hackerspace-silesia/Smogomierz/html/html-content.h

#ifdef ARDUINO_ARCH_ESP8266
#include <avr/pgmspace.h>
#endif

static const char WEB_PAGE_HEADER_CSS[] PROGMEM = "<link rel='stylesheet' href='https://rawcdn.githack.com/hackerspace-silesia/Smogomierz/b1e4dd9a2b6fddb63da88c46ef934509ab1def44/css/smogly.css'>";
// via http://raw.githack.com 
//static const char WEB_PAGE_HEADER_CSS[] PROGMEM = "<link rel='stylesheet' href='https://raw.githubusercontent.com/hackerspace-silesia/Smogomierz/master/css/smogly.css'>";
// https://raw.githubusercontent.com/hackerspace-silesia/Smogomierz/dev/src/css/smogly.css
// based on bootstrap.min.css - 4.4.1 and Bootswatch v4.4.1
// https://raw.githack.com

#ifdef ARDUINO_ARCH_ESP8266
const char WEB_PAGE_HEADER[] PROGMEM = R"rawliteral(<html lang='{Language}'><head><meta charset='utf-8'><meta name='viewport' content='width=device-width, initial-scale=1, shrink-to-fit=no'><title>Smogly - {CurrentPageTitle}</title>
{WEB_PAGE_CSS}
</head><body>
	<nav class='navbar navbar-expand-lg navbar-dark bg-dark' style='padding-left:15%'>
	<a class='navbar-brand' href='/'>Smogly</a>
	  <button class='navbar-toggler' type='button' data-toggle='collapse' data-target='#navbarColor02' aria-controls='navbarColor02' aria-expanded='false' aria-label='Toggle navigation'>
	  <span class='navbar-toggler-icon'></span>
	  </button>
	  <div class='collapse navbar-collapse' id='navbarColor02' style='padding-left:2rem'>
	    <ul class='navbar-nav mr-auto'>
	      <li class='nav-item'>
	        <a class='nav-link' href='/'>{IndexPageTitle}</a>
	      </li>
	      <li class='nav-item'>
	        <a class='nav-link' href='/config'>{ConfigPageTitle}</a>
	      </li>
		  <li class='nav-item'>
		  	<a class='nav-link' href='/update'>{UpdatePageTitle}</a>
		  </li>
	    </ul>
</div></nav>
		)rawliteral";

static const char SMOGLY_LOGO_URL[] PROGMEM = "<a class='navbar-brand' href='/'>Smogly</a>";

#elif defined ARDUINO_ARCH_ESP32
static const char WEB_PAGE_HEADER[] PROGMEM = R"rawliteral(<html lang='{Language}'><head><meta charset='utf-8'><meta name='viewport' content='width=device-width, initial-scale=1, shrink-to-fit=no'><title>Smogly - {CurrentPageTitle}</title>
{WEB_PAGE_CSS}
</head><body>
	<nav class='navbar navbar-expand-lg navbar-dark bg-dark' style='padding-left:15%'>
	<a class='navbar-brand' href='/'><img border='0' width='165' height='40' alt='SmoglyLogo' src='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'></a>
	  <button class='navbar-toggler' type='button' data-toggle='collapse' data-target='#navbarColor02' aria-controls='navbarColor02' aria-expanded='false' aria-label='Toggle navigation'>
	  <span class='navbar-toggler-icon'></span>
	  </button>
	  <div class='collapse navbar-collapse' id='navbarColor02' style='padding-left:2rem'>
	    <ul class='navbar-nav mr-auto'>
	      <li class='nav-item'>
	        <a class='nav-link' href='/'>{IndexPageTitle}</a>
	      </li>
	      <li class='nav-item'>
	        <a class='nav-link' href='/config'>{ConfigPageTitle}</a>
	      </li>
		  <li class='nav-item'>
		  	<a class='nav-link' href='/update'>{UpdatePageTitle}</a>
		  </li>
	    </ul>
</div></nav>
		)rawliteral";

static const char SMOGLY_LOGO_URL[] PROGMEM = "<a class='navbar-brand' href='/'><img border='0' width='165' height='40' alt='SmoglyLogo' src='https://raw.githubusercontent.com/hackerspace-silesia/Smogomierz/master/Smogly_Logo/SmoglyLogoTopMenu.png'></a>";
//"
#endif

#ifdef ARDUINO_ARCH_ESP8266
static const char WEB_PAGE_FOOTER[] PROGMEM = R"rawliteral(<br><hr><center><a href='http://smogly.org/' target='_blank'>Smogly</a> &#9830; <a href='https://hs-silesia.pl' target='_blank'>Hackerspace Silesia</a> &#9830;
	<script type='text/javascript'>
  		document.write(new Date().getFullYear());
	</script>
	</center></div></main></form>
			<script src='https://code.jquery.com/jquery-3.4.1.slim.min.js' integrity='sha384-J6qa4849blE2+poT4WnyKhv5vZF5SrPo0iEjwBvKU7imGFAV0wwj1yYfoRSJoZ+n' crossorigin='anonymous'></script>
			<script src='https://cdn.jsdelivr.net/npm/popper.js@1.16.0/dist/umd/popper.min.js' integrity='sha384-Q6E9RHvbIyZFJoft+2mJbHaEWldlvI9IOYy5n3zV9zzTtmI3UksdQRVvoxMfooAo' crossorigin='anonymous'></script>
			<script src='https://stackpath.bootstrapcdn.com/bootstrap/4.4.1/js/bootstrap.min.js' integrity='sha384-wfSDF2E50Y2D1uUdj0O3uMBJnjuUD4Ih7YwaYd1iqfktj0Uod8GCExl3Og8ifwB6' crossorigin='anonymous'></script>
			</body></html>
	)rawliteral";
#elif defined ARDUINO_ARCH_ESP32
static const char WEB_PAGE_FOOTER[] PROGMEM = R"rawliteral(<br><hr><center><a href='http://smogly.org/' target='_blank'>Smogly</a> &#9830; <a href='https://hs-silesia.pl' target='_blank'>Hackerspace Silesia</a> &#9830;
	<script type='text/javascript'>
  		document.write(new Date().getFullYear());
	</script>
	</center></div></main></form>
			<script src='https://code.jquery.com/jquery-3.4.1.slim.min.js' integrity='sha384-J6qa4849blE2+poT4WnyKhv5vZF5SrPo0iEjwBvKU7imGFAV0wwj1yYfoRSJoZ+n' crossorigin='anonymous'></script>
			<script src='https://cdn.jsdelivr.net/npm/popper.js@1.16.0/dist/umd/popper.min.js' integrity='sha384-Q6E9RHvbIyZFJoft+2mJbHaEWldlvI9IOYy5n3zV9zzTtmI3UksdQRVvoxMfooAo' crossorigin='anonymous'></script>
			<script src='https://stackpath.bootstrapcdn.com/bootstrap/4.4.1/js/bootstrap.min.js' integrity='sha384-wfSDF2E50Y2D1uUdj0O3uMBJnjuUD4Ih7YwaYd1iqfktj0Uod8GCExl3Og8ifwB6' crossorigin='anonymous'></script>
			</body></html>
	)rawliteral";
#endif
	
// CONFIG PAGE - Start
	const char WEB_CONFIG_PAGE_TOP[] PROGMEM = R"rawliteral(<main role='main' class='container'><div class='jumbotron'>
	<center><h1>Smogly - {TEXT_CONFIG_PAGE}</h1></center><br><br>
	)rawliteral";

	const char WEB_CONFIG_PAGE_SUBMIT_DEVICE_BUTTON[] = "<input type='submit' name='submit1' class='btn btn-outline-danger' value='{TEXT_SAVE}' /></form>";

	const char WEB_CONFIG_PAGE_SUBMIT_SERVICES_BUTTON[] = "<input type='submit' name='submit2' class='btn btn-outline-danger' value='{TEXT_SAVE}' /></form>";

	const char WEB_CONFIG_ADVANCED_MQTT_PAGE_SUBMIT_SERVICES_BUTTON[] = "<input type='submit' name='submit3' class='btn btn-outline-danger' value='{TEXT_SAVE}' /></form>";

	const char WEB_CONFIG_PAGE_SELECT[] PROGMEM = "<select name='{key}'>";

	const char WEB_CONFIG_PAGE_SELECTEND[] PROGMEM = "</select><br />";

	const char WEB_CONFIG_PAGE_ADDOPTION[] PROGMEM = "<option value='{value}' {srslyValue}{label}</option>";

	const char WEB_CONFIG_PAGE_TEXTIMPUT[] PROGMEM = "<input type='text' maxlength='255' size='20' name='{key}' value='{value}'> {postfix}<br />";

	const char WEB_CONFIG_PAGE_MQTT_TEXTIMPUT[] PROGMEM = "<input type='text' maxlength='120' size='32' name='{key}' value='{value}'>{postfix}";

	const char WEB_CONFIG_PAGE_PASSWDINPUT[] = "<input type='password' maxlength='255' size='20' name='{key}' value='{value}'> {postfix}<br />";

	const char WEB_CONFIG_PAGE_INTINPUT[] PROGMEM = "<input type='number' step='1' maxlength='255' name='{key}' value='{value}'> {postfix}<br />";

	const char WEB_CONFIG_PAGE_FLOATINPUT[] = "<input type='number' step='0.000001' maxlength='255' name='{key}' value='{value}'> {postfix}<br />";
	/*
	const char WEB_CONFIG_DEVICE_PAGE_BUTTON[] = "<a href='/config_device' class='btn btn-outline-primary btn-sm' role='button'>{TEXT_CONFIG_DEVICE_PAGE}</a>";

	const char WEB_CONFIG_SERVICES_PAGE_BUTTON[] = "<a href='/config_services' class='btn btn-outline-primary btn-sm' role='button'>{TEXT_CONFIG_SERVICES_PAGE}</a>";
	*/
	const char WEB_CONFIG_PAGE_WIFIERASE[] = "<a href='/erase_wifi' class='btn btn-outline-primary btn-sm' role='button'>{TEXT_ERASEWIFICONFIG}</a>";

	const char WEB_CONFIG_PAGE_HOMEKIT_RESET[] = "<a href='/homekit_reset' class='btn btn-outline-primary btn-sm' role='button'>{TEXT_PAGE_HOMEKIT_RESET}</a>";

	const char WEB_CONFIG_PAGE_RESTORECONFIG[] = "<a href='/restore_config' class='btn btn-outline-primary btn-sm' role='button'>{TEXT_RESTORESETTINGS}</a>";

	const char WEB_CONFIG_TOP_PAGE_INFO[] PROGMEM = R"rawliteral(<center><div class='card text-white bg-success mb-3' style='max-width: 30rem;'>
			  <div class='card-body'>
			    <h4 class='card-title'><strong>{TEXT_SAVED}!</strong></h4>
			    <p class='card-text'>{TEXT_POSTCONFIG_INFO}</p>
			  </div></div></center>)rawliteral";

// CONFIG PAGE - END
// CONFIG DEVICE PAGE - Start	
#ifdef ASYNC_WEBSERVER_ON
const char WEB_CONFIG_DEVICE_PAGE_TOP[] PROGMEM = R"rawliteral(<form method='GET' action='/config_device_save'>
	<main role='main' class='container'><div class='jumbotron'>
	<center><h1>Smogly - {TEXT_CONFIG_DEVICE_PAGE}</h1></center><br>
	<div style='color: #2f7a2d'> <strong>{TEXT_SAVED}!</strong> - {TEXT_POSTCONFIG_INFO} </div><br><hr><br>
	{TEXT_INSTRUCIONSLINK}<br><br>
	)rawliteral";
#else
const char WEB_CONFIG_DEVICE_PAGE_TOP[] PROGMEM = R"rawliteral(<form method='POST' action='/config_device'>
	<main role='main' class='container'><div class='jumbotron'>
	<center><h1>Smogly - {TEXT_CONFIG_DEVICE_PAGE}</h1></center><br>
	{WEB_CONFIG_TOP_PAGE_INFO}
	<br><hr><br>
	{TEXT_INSTRUCIONSLINK}<br><br>
	)rawliteral";
#endif
const char WEB_CONFIG_DEVICE_PAGE_SECOND_THP[] PROGMEM = R"rawliteral(
	<br>
	{TEXT_SECOND_THP_SDA_SCL} <br>
	<b>{TEXT_SECOND_THP_SDA}: </b>{SECOND_THP_SDA}
	<b>{TEXT_SECOND_THP_SCL}: </b>{SECOND_THP_SCL}
)rawliteral";

const char WEB_CONFIG_DEVICE_PAGE_CONFIG[] PROGMEM = R"rawliteral(<b>{TEXT_DEVICENAME}: </b>{device_name} <br>
	<b>{TEXT_DEVICENAMEAUTO}: </b>{DEVICENAME_AUTO}
	<b>{TEXT_SELECTEDLANGUAGE}: </b>{LanguageSelect}
	<hr>
	<b>{TEXT_TEMPHUMIPRESSSENSOR}: </b>{THP_MODELSelect}
	<b>{TEXT_PMSENSOR}: </b>{DUST_MODELSelect}
	<hr>{TEXT_FIRST_THP_SDA_SCL} - {THP_MODEL}<br>
	<b>{TEXT_FIRST_THP_SDA}: </b>{FIRST_THP_SDA}
	<b>{TEXT_FIRST_THP_SCL}: </b>{FIRST_THP_SCL}
	<br>
	<b>{TEXT_SECOND_THP}: </b>{SECOND_THP}
	{WEB_CONFIG_DEVICE_PAGE_SECOND_THP}
	<br>{TEXT_DUST_TX_RX} - {DUST_MODEL}<br>
	<b>{TEXT_DUST_TX}: </b>{DUST_TX}
	<b>{TEXT_DUST_RX}: </b>{DUST_RX}
	<hr>
	<b>{TEXT_FREQUENTMEASUREMENTONOFF}: </b>{FREQUENTMEASUREMENT_Select} {TEXT_FREQUENTMEASUREMENTINFO}<br>
	<b>{TEXT_MEASUREMENTFREQUENCY}: </b>{FREQUENTMEASUREMENT_time}
	<b>{TEXT_AVERAGELASTRESULT}: </b>{NUMBEROFMEASUREMENTS}
	<hr><b>DeepSleep: </b>{DEEPSLEEP_ON} {TEXT_DEEPSLEEPINFO}
	<hr>
	<b>{TEXT_DISPLAYPM1}: </b> {DISPLAY_PM1}
	<b>{TEXT_ALTITUDEINFO}: </b>{MYALTITUDE}
	<hr>
	<b>{TEXT_SECURECONFIGUPDATEPAGE}: </b>{CONFIG_AUTH}
	<b>{TEXT_SECURELOGIN}: </b>{CONFIG_USERNAME}
	<b>{TEXT_SECUREPASSWD}: </b>{CONFIG_PASSWORD}
	{TEXT_SECURELOGOUTINFO}
	<hr>
	<b>Debug: </b>{DEBUG}
	<b>{TEXT_CALIBMETHOD}: </b>{CalibrationModelSelect}
	<b>{TEXT_CALIB1}: </b>{calib1}
	<br>
	<!-- <b>{TEXT_CALIB2}: </b>{calib2} -->
	<b>{TEXT_SOFTWATEVERSION}: </b>{SOFTWAREVERSION}
	<br><b>{TEXT_AUTOUPDATEON}: </b>{AUTOUPDATEON} {TEXT_UPDATEPAGEAUTOUPDATEWARNING}
	<br><b>{TEXT_HOMEKIT_SUPPORT}: </b>{HOMEKIT_SUPPORT_ON}
	<b>{TEXT_HOMEKIT_IS_PAIRED}: </b>{HOMEKIT_PAIRED_RESET}
	
	<hr><center><br>
	{WiFiEraseButton}  {RestoreConfigButton}
	<br><br></center><hr><br><center>
	{SubmitButton}
	</center>
	)rawliteral";
// CONFIG DEVICE PAGE - END
// CONFIG SERVICES PAGE - Start
#ifndef ASYNC_WEBSERVER_ON
const char WEB_CONFIG_SERVICES_PAGE_TOP[] PROGMEM = R"rawliteral(<form method='POST' action='/config_services'>
	<main role='main' class='container'><div class='jumbotron'>
	<center><h1>Smogly - {TEXT_CONFIG_SERVICES_PAGE}</h1></center><br>
	{WEB_CONFIG_TOP_PAGE_INFO}
	<br><hr><br>
	{TEXT_INSTRUCIONSLINK}<br><br>
	)rawliteral";

	const char WEB_CONFIG_SERVICES_PAGE_CONFIG[] PROGMEM = R"rawliteral(<b>{TEXT_SENDINGINTERVAL}: </b>{SENDING_FREQUENCY}
		<b>{TEXT_DBSENDINGINTERVAL}: </b>{SENDING_DB_FREQUENCY}
		<hr>
		<b>{TEXT_SMOGLISTSENDING}: </b>{SMOGLIST_ON} {TEXT_SMOGLISTINFO}
		<hr>
		<b>{TEXT_LUFTDATENSENDING}: </b>{LUFTDATEN_ON}
		<b>ChipID: </b>{LUFTDATEN_ChipID}
		<br><b>{THPSENSOR}</b> Sensor PIN: <b>{THPXPIN}</b>
		<br><b>{DUSTSENSOR}</b> Sensor PIN: <b>{DUSTXPIN}</b>
		<hr>
		<b>{TEXT_AQIECOSENDING}: </b>{AQI_ECO_ON}
		<b>{TEXT_AQIECOSERVER}: </b>{AQI_ECO_HOST}
		<b>{TEXT_AQIECOPATH}: </b>{AQI_ECO_PATH}
		<b>{ESP_MODEL} ID: </b>{AQI_ECO_ChipID}
		<hr>
		<b>{TEXT_AIRMONITORSENDING}: </b>{AIRMONITOR_ON}
		<b>{TEXT_AIRMONITORCHARTS}: </b>{AIRMONITOR_GRAPH_ON}
		<b>{TEXT_AIRMONITORCOORDINATESINFO}:
		<br>{TEXT_AIRMONITORLATITUDE}: </b>{LATITUDE}
		<b>{TEXT_AIRMONITORLONGITUDE}: </b>{LONGITUDE}
		<hr>
		<b>{TEXT_THINGSPEAKSENDING}: </b>{THINGSPEAK_ON}
		<b>{TEXT_THINGSPEAKCHARTS}: </b>{THINGSPEAK_GRAPH_ON}
		<b>{TEXT_THINGSPEAK_WRITE_API_KEY}: </b>{THINGSPEAK_API_KEY}
		<b>{TEXT_THINGSPEAKCHANNELID}: </b>{THINGSPEAK_CHANNEL_ID}
		<b>{TEXT_THINGSPEAK_READ_API_KEY}: </b>{THINGSPEAK_READ_API_KEY}
		<hr>
		<b>{TEXT_INFLUXDBSENDING}: </b>{INFLUXDB_ON}
		<b>{TEXT_INFLUXDBVERSION}: </b>{INFLUXDB_VERSION}
		<b>{TEXT_INFLUXDBSERVER}: </b>{INFLUXDB_HOST}
		<b>{TEXT_INFLUXDBPORT}: </b>{INFLUXDB_PORT}
		<b>{TEXT_INFLUXDBNAME}: </b>{INFLUXDB_DATABASE}
		<b>{TEXT_INFLUXDBUSER}: </b>{INFLUXDB_USER}
		<b>{TEXT_INFLUXDBPASSWD}: </b>{INFLUXDB_PASSWORD}
		<b>{TEXT_INFLUXDBORG}: </b>{INFLUXDB_ORG}
		<b>{TEXT_INFLUXDBBUCKET}: </b>{INFLUXDB_BUCKET}
		<b>{TEXT_INFLUXDBTOKEN}: </b>{INFLUXDB_TOKEN}
		<hr>
		<br><center>{AdvancedMQTTConfigButton}</center><br>
		<hr><center><br>
		{WiFiEraseButton}  {RestoreConfigButton}
		<br><br></center><hr><br><center>
		{SubmitButton}
		</center>
		)rawliteral";
#endif
// CONFIG SERVICES PAGE - END
// CONFIG ADVANCED MQTT PAGE - Start
#ifdef ASYNC_WEBSERVER_ON
	const char WEB_CONFIG_ADVANCED_MQTT_PAGE_TOP[] PROGMEM = R"rawliteral(<form method='GET' action='/config_adv_mqtt_save'>
	<main role='main' class='container'><div class='jumbotron'>
	<center><h1>Smogly - {TEXT_ADVANCED_MQTT_PAGE}</h1></center><br>
	{WEB_CONFIG_TOP_PAGE_INFO}
	<br><hr><br>
	{TEXT_INSTRUCIONSLINK}<br><br>
	)rawliteral";
#else
	const char WEB_CONFIG_ADVANCED_MQTT_PAGE_TOP[] PROGMEM = R"rawliteral(<form method='POST' action='/config_adv_mqtt'>
	<main role='main' class='container'><div class='jumbotron'>
	<center><h1>Smogly - {TEXT_ADVANCED_MQTT_PAGE}</h1></center><br>
	{WEB_CONFIG_TOP_PAGE_INFO}
	<br><hr><br>
	{TEXT_INSTRUCIONSLINK}<br><br>
	)rawliteral";
#endif

	const char WEB_CONFIG_ADVANCED_MQTT_PAGE_CONFIG[] PROGMEM = R"rawliteral(<br><b>{TEXT_MQTTSENDING}: </b>{MQTT_ON}
		<b>{TEXT_MQTTSERVER}: </b>{MQTT_HOST}
		<b>{TEXT_MQTTPORT}: </b>{MQTT_PORT}
		<b>{TEXT_MQTTUSER}: </b>{MQTT_USER}
		<b>{TEXT_MQTTPASSWD}: </b>{MQTT_PASSWORD}
		<br>{TEXT_MQTT_TOPIC_INFO}
		<br><br>
		<b>{TEXT_MQTT_IP_IN_TOPIC}: </b>{MQTT_IP_IN_TOPIC}
		<b>{TEXT_MQTT_DEVICENAME_IN_TOPIC}: </b>{MQTT_DEVICENAME_IN_TOPIC}
		<b>{TEXT_MQTT_SLASH_AT_THE_BEGINNING}: </b>{MQTT_SLASH_AT_THE_BEGINNING}
		<b>{TEXT_MQTT_SLASH_AT_THE_END}: </b>{MQTT_SLASH_AT_THE_END}
		<br>
		<b>{TEXT_TEMP_TOPIC}: </b>/{MQTT_IP}{MQTT_DEVICENAME}{MQTT_TOPIC_TEMP}/{MQTT_TEMP}<br />
		<b>{TEXT_HUMI_TOPIC}: </b>/{MQTT_IP}{MQTT_DEVICENAME}{MQTT_TOPIC_HUMI}/{MQTT_HUMI}<br />
		<b>{TEXT_PRESS_TOPIC}: </b>/{MQTT_IP}{MQTT_DEVICENAME}{MQTT_TOPIC_PRESS}/{MQTT_PRESS}<br />
		<b>{TEXT_PM1_TOPIC}: </b>/{MQTT_IP}{MQTT_DEVICENAME}{MQTT_TOPIC_PM1}/{MQTT_PM1}<br />
		<b>{TEXT_PM25_TOPIC}: </b>/{MQTT_IP}{MQTT_DEVICENAME}{MQTT_TOPIC_PM25}/{MQTT_PM25}<br />
		<b>{TEXT_PM10_TOPIC}: </b>/{MQTT_IP}{MQTT_DEVICENAME}{MQTT_TOPIC_PM10}/{MQTT_PM10}<br />
		<b>{TEXT_AIRQUALITY_TOPIC}: </b>/{MQTT_IP}{MQTT_DEVICENAME}{MQTT_TOPIC_AIRQUALITY}/{MQTT_AIRQUALITY}<br />
		<br>
		<hr><center><br>
		{RestoreConfigButton}
		<br><br></center><hr><br><center>
		{SubmitButton}
		</center>
		)rawliteral";
		//#endif
// CONFIG ADVANCED MQTT PAGE - END
// UPDATE BUTTONS - START

const char WEB_GOTO_CONFIG_ADVANCED_MQTT_PAGE_BUTTON[] PROGMEM = "<a href='/config_adv_mqtt' class='btn btn-outline-primary btn-sm' role='button'>{TEXT_CONFIG_ADV_MQTT}</a>";

const char WEB_UPDATE_BUTTON_MANUALUPDATE[] PROGMEM = "<a href='/update' class='btn btn-outline-primary btn-sm' role='button'>{TEXT_MANUALUPDATEBUTTON}</a>";

// UPDATE BUTTONS - END
// UPDATE PAGE - START
#ifndef ASYNC_WEBSERVER_ON
const char WEB_UPDATE_PAGE_UPDATE[] PROGMEM = R"rawliteral(<main role='main' class='container'><div class='jumbotron'>
	<form id='data' action='/update' method='POST' enctype='multipart/form-data'>
	<center><h1>Smogly - {TEXT_UPDATE_PAGE}</h1></center><br><br>
	{WEB_UPDATE_INFO_WARNING}
	<br><br><div class='input-group mb-3'><div class='custom-file'><input type='file' accept='.bin' class='custom-file-input' id='inputGroupFile04' name='update'><label class='custom-file-label' for='inputGroupFile04'>{TEXT_SELECTUPDATEFILE}</label></div><div class='input-group-append'><button class='btn btn-danger' type='submit'>{TEXT_SUBMITUPDATE}</button></div></div></form>
	<br>
	{TEXT_AUTOUPDATEON}: <b>{AUTOUPDATEONSTATUS}</b>
	<br>{TEXT_CURRENTSOFTVERSION}: <b>{SOFTWAREVERSION}</b>
	<br>{TEXT_SERVERSOFTWAREVERSION}: <b>{SERVERSOFTWAREVERSION}</b>
	<br>{TEXT_LATESTAVAILABLESOFT}
	<br>
	<br>{TEXT_CONNECTEDWIFI}: <b>{WiFiSSID}</b>
	<br>{TEXT_WIFIRSSI}: <b>{WiFiRSSI}</b>
	<br>{TEXT_WIFIQUALITY}: <b>{WiFiQuality}</b>
)rawliteral";
#endif
// UPDATE PAGE - END


#ifdef ARDUINO_ARCH_ESP8266
static char GITHUB_LINK[] = "<a title='Instructions' href='https://github.com/hackerspace-silesia/Smogomierz#instrukcje' target='_blank'>{TEXT_HERE}</a>";
static char WSPOLRZEDNE_GPS_LINK[] = "<a title='wspolrzedne-gps.pl' href='https://www.wspolrzedne-gps.pl' target='_blank'>{TEXT_HERE}</a>";
static char LUFTDATEN_LINK[] = "<a title='Sensor.Community' href='https://maps.sensor.community/#7/52.000/19.000' target='_blank'>Sensor.Community</a>";
static char LUFTDATENFORM_LINK[] = "<a title='devices.sensor.community' href='https://devices.sensor.community' target='_blank'>devices.sensor.community</a>";
static char SMOGLIST_LINK[] = "<a title='smoglist.pl' href='http://smoglist.pl' target='_blank'>Smoglist</a>";
static char AIRMONITOR_LINK[] = "<a title='AirMonitor' href='https://airmonitor.pl/prod/mapa' target='_blank'>AirMonitor</a>";
static char AIRMONITORFORM_LINK[] = "<a title='AirMonitor Form' href='https://airmonitor.pl/prod/station_registration' target='_blank'>{TEXT_THEFORM}</a>";
static char LATLONG_LINK[] = "<a title='latlong.net' href='https://www.latlong.net' target='_blank'>{TEXT_HERE}</a>";
static char THINGSPEAK_LINK[] = "<a title='ThingSpeak' href='https://thingspeak.com' target='_blank'>ThingSpeak</a>";
static char SMOGOMIERZRELEASES_LINK[] = "<b><a target='_blank' href='https://github.com/hackerspace-silesia/Smogomierz/releases'>{TEXT_HERE}</a></b>";
static char MADAVI_LINK[] = "<a title='madavi.de' href='https://www.madavi.de/sensor/graph.php' target='_blank'>{TEXT_HERE}</a>";
#elif defined ARDUINO_ARCH_ESP32
static char GITHUB_LINK[] = "<a title='Instructions' href='https://github.com/hackerspace-silesia/Smogomierz#instrukcje' target='_blank'>{TEXT_HERE}</a>";
static char WSPOLRZEDNE_GPS_LINK[] = "<a title='wspolrzedne-gps.pl' href='https://www.wspolrzedne-gps.pl' target='_blank'>{TEXT_HERE}</a>";
static char LUFTDATEN_LINK[] = "<a title='Sensor.Community' href='https://maps.sensor.community/#7/52.000/19.000' target='_blank'>Sensor.Community</a>";
static char LUFTDATENFORM_LINK[] = "<a title='devices.sensor.community' href='https://devices.sensor.community' target='_blank'>devices.sensor.community</a>";
static char SMOGLIST_LINK[] = "<a title='smoglist.pl' href='http://smoglist.pl' target='_blank'>Smoglist</a>";
static char AIRMONITOR_LINK[] = "<a title='AirMonitor' href='https://airmonitor.pl/prod/mapa' target='_blank'>AirMonitor</a>";
static char AIRMONITORFORM_LINK[] = "<a title='AirMonitor Form' href='https://airmonitor.pl/prod/station_registration' target='_blank'>{TEXT_THEFORM}</a>";
static char LATLONG_LINK[] = "<a title='latlong.net' href='https://www.latlong.net' target='_blank'>{TEXT_HERE}</a>";
static char THINGSPEAK_LINK[] = "<a title='ThingSpeak' href='https://thingspeak.com' target='_blank'>ThingSpeak</a>";
static char SMOGOMIERZRELEASES_LINK[] = "<b><a target='_blank' href='https://github.com/hackerspace-silesia/Smogomierz/releases'>{TEXT_HERE}</a></b>";
static char MADAVI_LINK[] = "<a title='madavi.de' href='https://www.madavi.de/sensor/graph.php' target='_blank'>{TEXT_HERE}</a>";
#endif
