hackerspace-silesia/Smogomierz/src/WiFiManager/WiFiManager_strings_en.h

/**
 * strings_en.h
 * engligh strings for
 * WiFiManager, a library for the ESP8266/Arduino platform
 * for configuration of WiFi credentials using a Captive Portal
 *
 * @author Creator tzapu
 * @author tablatronix
 * @version 0.0.0
 * @license MIT
 */

#ifndef _WM_STRINGS_H_
#define _WM_STRINGS_H_

#ifndef WIFI_MANAGER_OVERRIDE_STRINGS
// !!! THIS DOES NOT WORK, you cannot define in a sketch, if anyone one knows how to order includes to be able to do this help!

const char HTTP_HEAD_START[]       PROGMEM = "<!DOCTYPE html><html lang='en'><head><meta name='format-detection' content='telephone=no'><meta charset='UTF-8'><meta  name='viewport' content='width=device-width,initial-scale=1,user-scalable=no'/><title>{v}</title>";
const char HTTP_SCRIPT[]           PROGMEM = "<script>function c(l){"
"document.getElementById('s').value=l.innerText||l.textContent;"
"p = l.nextElementSibling.classList.contains('l');"
"alert(p);"
"document.getElementById('p').disabled = !p;"
"if(p)document.getElementById('p').focus();}</script>";

const char HTTP_HEAD_END[]         PROGMEM = "</head><body class='{c}'><div class='wrap'>";

const char HTTP_ROOT_MAIN[]        PROGMEM = "<h1>{v}</h1><h3></h3>";
const char * const HTTP_PORTAL_MENU[] PROGMEM = {
"<form action='/wifi'    method='get'><button><center>Podłącz do WiFi <br> WiFi Config</center></button></form><br/>\n", // MENU_WIFI
//"<form action='/0wifi'   method='get'><button>Skonfiguruj WiFi (No Scan)</button></form><br/>\n", // MENU_WIFINOSCAN
//"<form action='/info'    method='get'><button>Instrukcja obsługi</button></form><br/>\n", // MENU_INFO
//"<form action='/param'   method='get'><button>Setup</button></form><br/>\n",//MENU_PARAM
"<form action='/close'   method='get'><button><center>Zamknij <br> Close</center></button></form><br/>\n", // MENU_CLOSE
"<form action='/restart' method='get'><button><center>Uruchom ponownie <br> Restart</center></button></form><br/>\n",// MENU_RESTART
//"<form action='/exit'    method='get'><button>Exit / Zakończ</button></form><br/>\n",  // MENU_EXIT
//"<form action='/erase'   method='get'><button class='D'>Erase / Wyzeruj</button></form><br/>\n", // MENU_ERASE
"<hr><br/>" // MENU_SEP
};

// const char HTTP_PORTAL_OPTIONS[]   PROGMEM = strcat(HTTP_PORTAL_MENU[0] , HTTP_PORTAL_MENU[3] , HTTP_PORTAL_MENU[7]);
const char HTTP_PORTAL_OPTIONS[]   PROGMEM = "";
const char HTTP_ITEM_QI[]          PROGMEM = "<div role='img' aria-label='{r}%' title='{r}%' class='q q-{q} {i} {h}'></div>"; // rssi icons
const char HTTP_ITEM_QP[]          PROGMEM = "<div class='q {h}'>{r}%</div>"; // rssi percentage
const char HTTP_ITEM[]             PROGMEM = "<div><a href='#p' onclick='c(this)'>{v}</a>{qi}{qp}</div>"; // {q} = HTTP_ITEM_QI, {r} = HTTP_ITEM_QP
// const char HTTP_ITEM[]            PROGMEM = "<div><a href='#p' onclick='c(this)'>{v}</a> {R} {r}% {q} {e}</div>"; // test all tokens

const char HTTP_FORM_START[]       PROGMEM = "<form method='POST' action='{v}'>";
const char HTTP_FORM_WIFI[]        PROGMEM = "<label for='s'>WiFi</label><input id='s' name='s' maxlength='32' autocorrect='off' autocapitalize='none' placeholder='{v}'><br/><label for='p'>Password</label><input id='p' name='p' maxlength='64' type='password' placeholder='{p}'>";

const char HTTP_FORM_WIFI_END[]    PROGMEM = "";
const char HTTP_FORM_STATIC_HEAD[] PROGMEM = "<hr><br/>";
const char HTTP_FORM_END[]         PROGMEM = "<br/><br/><button type='submit'><center>Zapisz <br> Save</center></button></form>";
const char HTTP_FORM_LABEL[]       PROGMEM = "<label for='{i}'>{t}</label>";
const char HTTP_FORM_PARAM_HEAD[]  PROGMEM = "<hr><br/>";
const char HTTP_FORM_PARAM[]       PROGMEM = "<br/><input id='{i}' name='{n}' maxlength='{l}' value='{v}' {c}>";

const char HTTP_SCAN_LINK[]        PROGMEM = "<br/><form action='/wifi?refresh=1' method='POST'><button name='refresh' value='1'><center>Odśwież <br> Refresh</center></button></form>";
const char HTTP_SAVED[]            PROGMEM = "<div class='msg'></center><strong>PL:</strong><br>Zapisano ustawienia<br />Za chwilę nastąpi restart Smogly. Jeśli nie uda się połączyć z siecią WiFi - spróbuj ponownie skonfigurować urządzenie.<br><br><strong>EN:</strong><br>Saving Credentials<br/>Trying to connect Smogly to network.<br/>If it fails reconnect - try again</div>";

const char HTTP_PARAMSAVED[]       PROGMEM = "<div class='msg'>Zapisano <br> Saved<br/></div>";
const char HTTP_END[]              PROGMEM = R"rawliteral(</div><br><hr><center>Smogly &#9830;
	<script type='text/javascript'>
  		document.write(new Date().getFullYear());
	</script>
	</center></body></html>)rawliteral";
const char HTTP_ERASEBTN[]         PROGMEM = "<br/><form action='/erase' method='get'><button class='D'>Erase WiFi Config / Wyzeruj ustawienia WiFi</button></form>";

const char HTTP_UPDATEBTN[]        PROGMEM = "<br/><form action='/update' method='get'><button>Update</button></form>";
const char HTTP_BACKBTN[]          PROGMEM = "<hr><br/><form action='/' method='get'><button>Back</button></form>";
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
